headblockhead/IN-12NixieClock/images/pcbGuide3.jpg

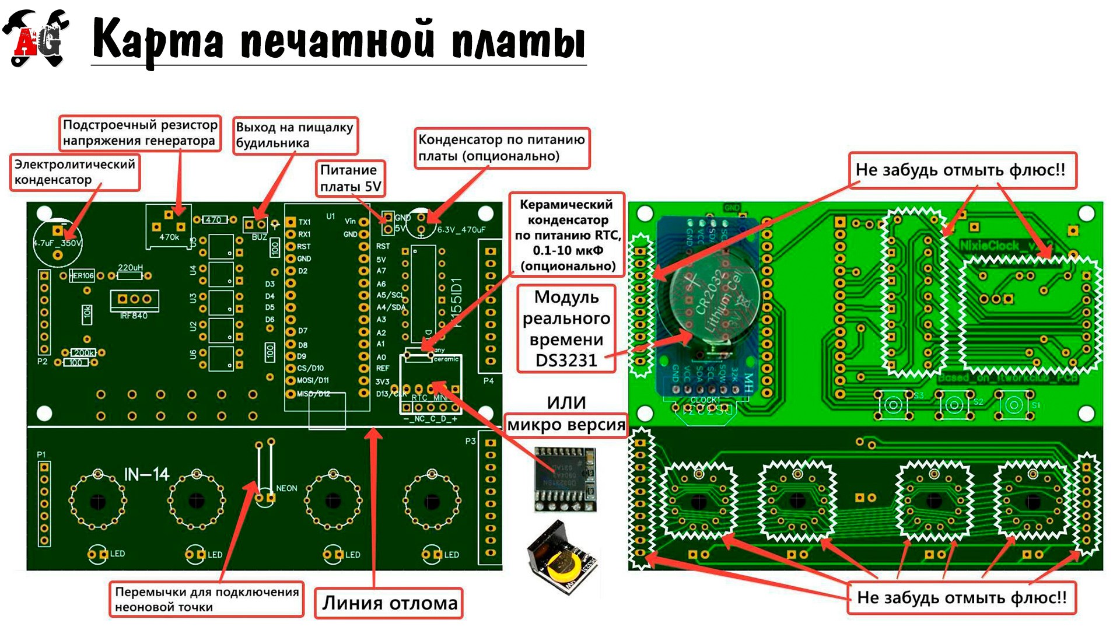
images/pcbGuide3.jpg
